iqyx/rfamp/pcb/rev1/output/rfamp-bot1.png

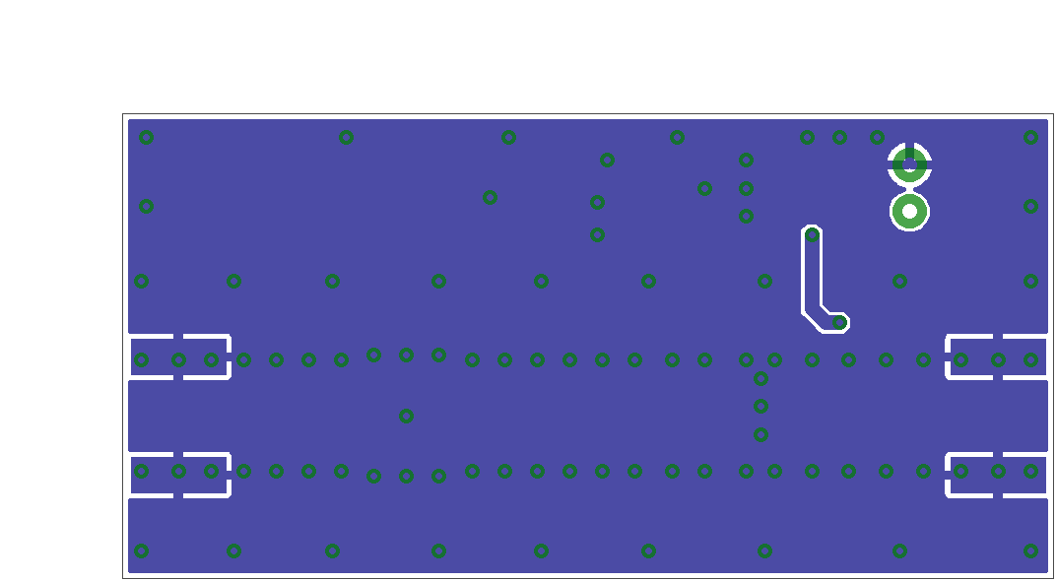
pcb/rev1/output/rfamp-bot1.png
