iqyx/rfamp/pcb/rev1/output/rfamp-botsilk1.png

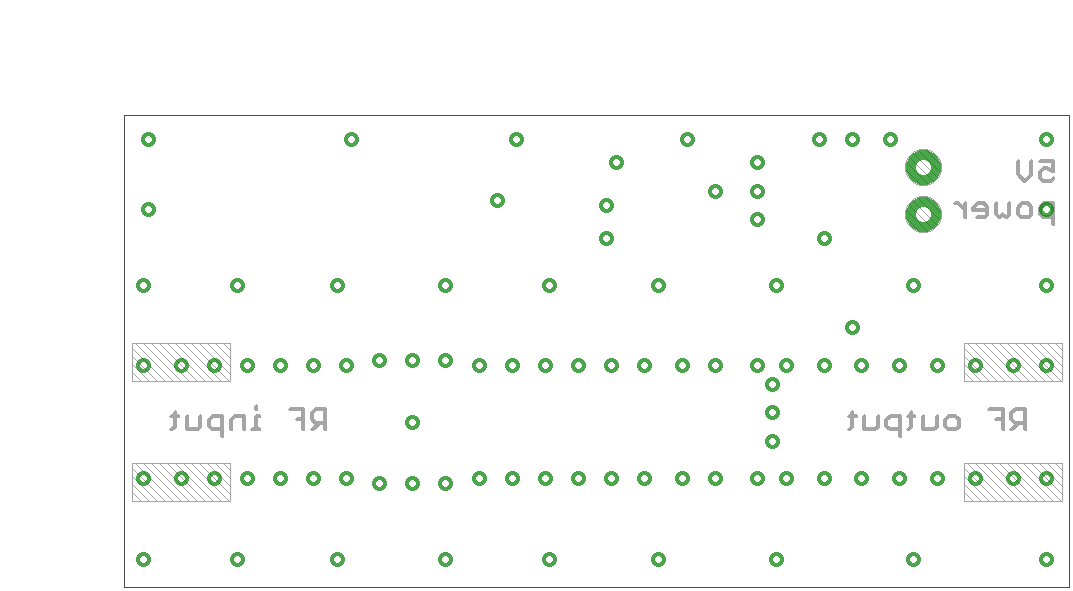
pcb/rev1/output/rfamp-botsilk1.png
