iqyx/rfamp/pcb/rev1/output/rfamp-placement1.png

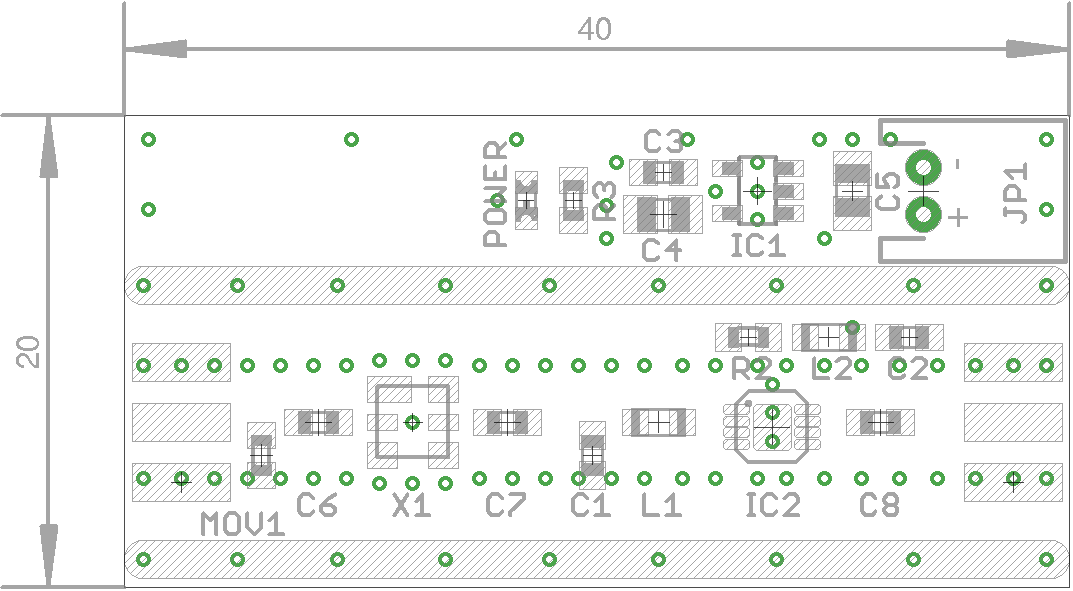
pcb/rev1/output/rfamp-placement1.png
