iqyx/rfamp/pcb/rev1/output/rfamp-sch1.png

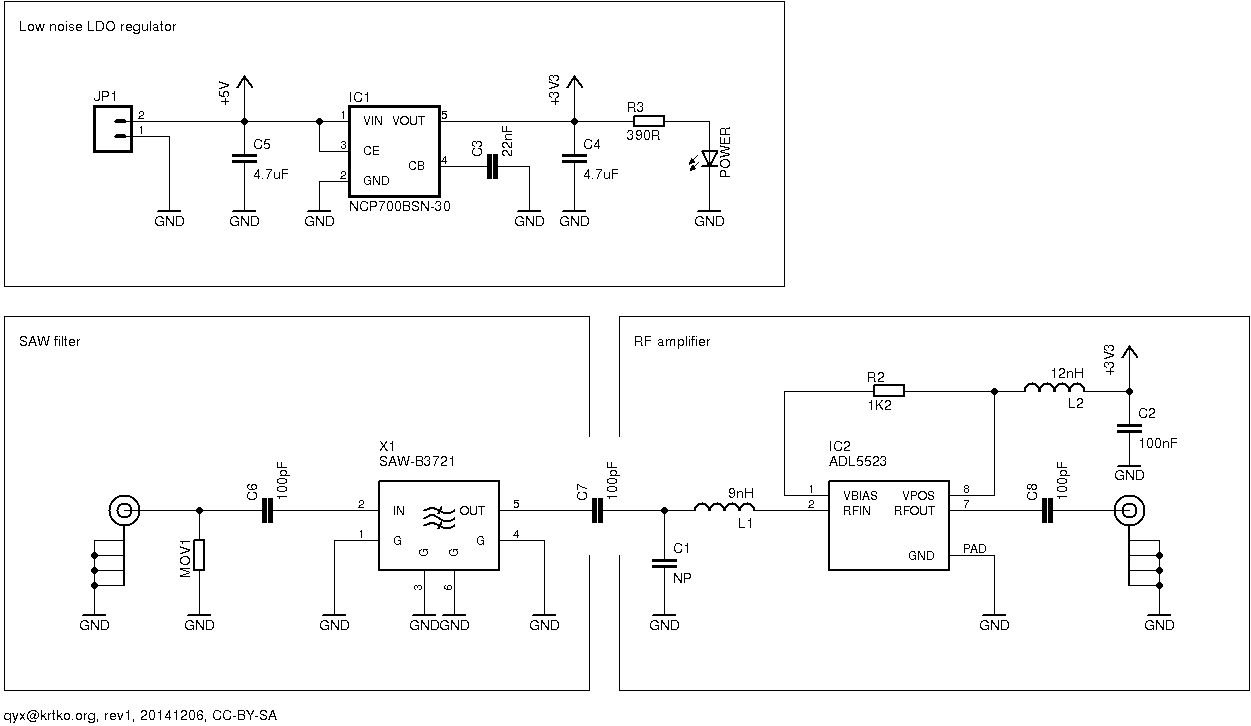
pcb/rev1/output/rfamp-sch1.png
