iqyx/rfamp/pcb/rev1/output/rfamp-top1.png

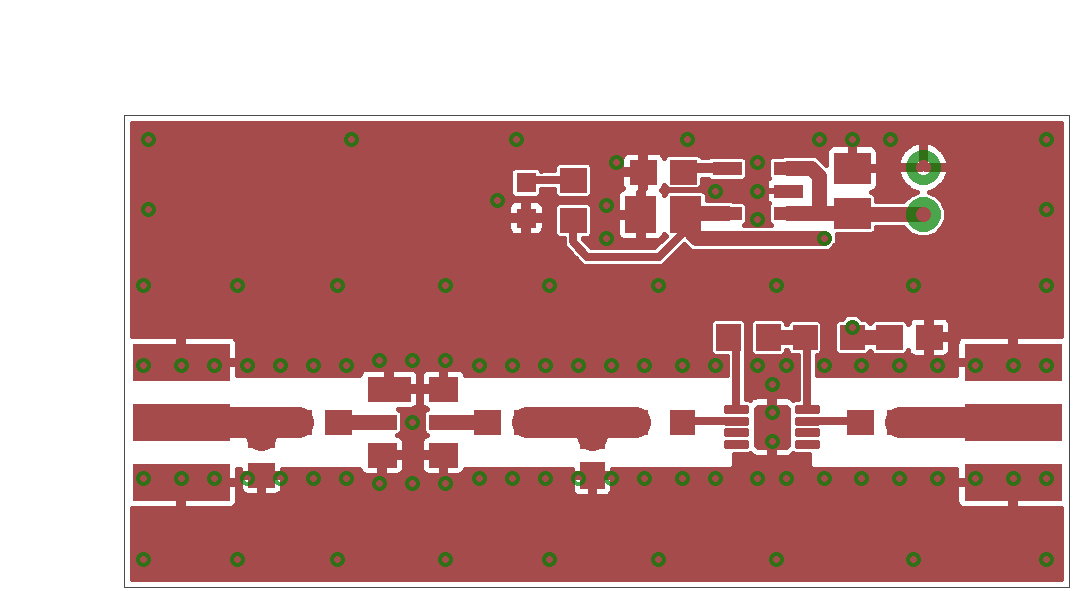
pcb/rev1/output/rfamp-top1.png
